bleeptrack/picoplanet/example/platformio/variants/bleeptrack_picoplanet/variant.h

/*
  Copyright (c) 2014-2015 Arduino LLC.  All right reserved.

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
  You should have received a copy of the GNU Lesser General Public
  License along with this library; if not, write to the Free Software
  Foundation, Inc., 51 Franklin St, Fifth Floor, Boston, MA  02110-1301  USA
*/

#ifndef _VARIANT_ARDUINO_ZERO_
#define _VARIANT_ARDUINO_ZERO_

// The definitions here needs a SAMD core >=1.6.6
#define ARDUINO_SAMD_VARIANT_COMPLIANCE 10606

/*----------------------------------------------------------------------------
 *        Definitions
 *----------------------------------------------------------------------------*/

/** Frequency of the board main oscillator */
#define VARIANT_MAINOSC		(32768ul)

/** Master clock frequency */
#define VARIANT_MCK	(F_CPU)

/*----------------------------------------------------------------------------
 *        Headers
 *----------------------------------------------------------------------------*/

#include "WVariant.h"

#ifdef __cplusplus
#include "SERCOM.h"
#include "Uart.h"
#endif // __cplusplus

#ifdef __cplusplus
extern "C"
{
#endif // __cplusplus

/*----------------------------------------------------------------------------
 *        Pins
 *----------------------------------------------------------------------------*/

// Number of pins defined in PinDescription array
#define PINS_COUNT           (22u)
#define NUM_DIGITAL_PINS     (22u)
#define NUM_ANALOG_INPUTS    (5u)
#define NUM_ANALOG_OUTPUTS   (1u)
#define analogInputToDigitalPin(p)  ((p < 5u) ? (p) + PIN_A0 : -1)

#define digitalPinToPort(P)        ( &(PORT->Group[g_APinDescription[P].ulPort]) )
#define digitalPinToBitMask(P)     ( 1 << g_APinDescription[P].ulPin )
//#define analogInPinToBit(P)        ( )
#define portOutputRegister(port)   ( &(port->OUT.reg) )
#define portInputRegister(port)    ( &(port->IN.reg) )
#define portModeRegister(port)     ( &(port->DIR.reg) )
#define digitalPinHasPWM(P)        ( g_APinDescription[P].ulPWMChannel != NOT_ON_PWM || g_APinDescription[P].ulTCChannel != NOT_ON_TIMER )

/*
 * digitalPinToTimer(..) is AVR-specific and is not defined for SAMD
 * architecture. If you need to check if a pin supports PWM you must
 * use digitalPinHasPWM(..).
 *
 * https://github.com/arduino/Arduino/issues/1833
 */
// #define digitalPinToTimer(P)

// PINs
#define PIN_D1                   (1u)
#define PIN_D2                   (2u)
#define PIN_D3                   (3u)
#define PIN_D4                   (4u)
#define PIN_D5                   (5u)
#define PIN_D6                   (6u)
#define PIN_D7                   (7u)
#define PIN_NC                   (0u)
#define PIN_SWCLK                (19u)
#define PIN_SWDIO                (20u)

static const uint8_t D1  = PIN_D1;
static const uint8_t D2  = PIN_D2;
static const uint8_t D3  = PIN_D3;
static const uint8_t D4  = PIN_D4;
static const uint8_t D5  = PIN_D5;
static const uint8_t D6  = PIN_D6;
static const uint8_t D7  = PIN_D7;
static const uint8_t SWCLK  = PIN_SWCLK;
static const uint8_t SWDIO  = PIN_SWDIO;

// LEDs
#define PIN_LED_G            PIN_D5
#define PIN_LED_R            PIN_D6
#define PIN_LED_B            PIN_D7
#define PIN_LED_13           PIN_LED_R
#define PIN_LED_RXL          PIN_NC // or LED_x if you want it to flash with Serial()
#define PIN_LED_TXL          PIN_NC // or LED_x if you want it to flash with Serial()
#define PIN_LED              PIN_LED_R
#define PIN_LED2             PIN_LED_G
#define PIN_LED3             PIN_LED_B
#define LED_BUILTIN          PIN_LED_R

static const uint8_t LED_R  = PIN_LED_R;
static const uint8_t LED_G  = PIN_LED_G;
static const uint8_t LED_B  = PIN_LED_B;


/*
 * Analog pins
 */
#define PIN_A0               (8ul)
#define PIN_A1               (PIN_A0 + 1)
#define PIN_A2               (PIN_A0 + 2)
#define PIN_A3               (PIN_A0 + 3)
#define PIN_A4               (PIN_A0 + 4)
#define PIN_DAC0             PIN_A0
#define TOUCH1               PIN_A0
#define TOUCH2               PIN_A1
#define TOUCH3               PIN_A2

static const uint8_t A0  = PIN_A0;
static const uint8_t A1  = PIN_A1;
static const uint8_t A2  = PIN_A2;
static const uint8_t A3  = PIN_A3;
static const uint8_t A4  = PIN_A4;
static const uint8_t DAC0 = PIN_DAC0;

#define ADC_RESOLUTION		12

/*
 * Serial interfaces
 */

// Serial1 (sercom 0)
#define PIN_SERIAL1_RX       (22u)
#define PAD_SERIAL1_RX       SERCOM_RX_PAD_1
#define PIN_SERIAL1_TX       (21u)
#define PAD_SERIAL1_TX       UART_TX_PAD_0

/*
 * SPI Interfaces
 */
#define SPI_INTERFACES_COUNT 1

#define PIN_SPI_MISO         (19u)
#define PIN_SPI_MOSI         (3u)
#define PIN_SPI_SCK          (4u)
#define PERIPH_SPI           sercom1
#define PAD_SPI_TX           SPI_PAD_0_SCK_1
#define PAD_SPI_RX           SERCOM_RX_PAD_2

static const uint8_t SS	  = PIN_NC ;
static const uint8_t MOSI = PIN_SPI_MOSI ;
static const uint8_t MISO = PIN_SPI_MISO ;
static const uint8_t SCK  = PIN_SPI_SCK ;

/*
 * Wire Interfaces
 */
#define WIRE_INTERFACES_COUNT 1

#define PIN_WIRE_SDA         (1u)
#define PIN_WIRE_SCL         (2u)
#define PERIPH_WIRE          sercom2
#define WIRE_IT_HANDLER      SERCOM2_Handler

static const uint8_t SDA = PIN_WIRE_SDA;
static const uint8_t SCL = PIN_WIRE_SCL;

/*
 * USB
 */
#define PIN_USB_HOST_ENABLE (16ul)
#define PIN_USB_DM          (17ul)
#define PIN_USB_DP          (18ul)

#ifdef __cplusplus
}
#endif

/*----------------------------------------------------------------------------
 *        Arduino objects - C++ only
 *----------------------------------------------------------------------------*/

#ifdef __cplusplus

/*	=========================
 *	===== SERCOM DEFINITION
 *	=========================
*/
extern SERCOM sercom0;
extern SERCOM sercom1;
extern SERCOM sercom2;
extern SERCOM sercom3;

extern Uart Serial1;

#endif

// These serial port names are intended to allow libraries and architecture-neutral
// sketches to automatically default to the correct port name for a particular type
// of use.  For example, a GPS module would normally connect to SERIAL_PORT_HARDWARE_OPEN,
// the first hardware serial port whose RX/TX pins are not dedicated to another use.
//
// SERIAL_PORT_MONITOR        Port which normally prints to the Arduino Serial Monitor
//
// SERIAL_PORT_USBVIRTUAL     Port which is USB virtual serial
//
// SERIAL_PORT_LINUXBRIDGE    Port which connects to a Linux system via Bridge library
//
// SERIAL_PORT_HARDWARE       Hardware serial port, physical RX & TX pins.
//
// SERIAL_PORT_HARDWARE_OPEN  Hardware serial ports which are open for use.  Their RX & TX
//                            pins are NOT connected to anything by default.
#define SERIAL_PORT_USBVIRTUAL      Serial
#define SERIAL_PORT_MONITOR         Serial
// Serial has no physical pins broken out, so it's not listed as HARDWARE port
#define SERIAL_PORT_HARDWARE        Serial1
#define SERIAL_PORT_HARDWARE_OPEN   Serial1

#endif /* _VARIANT_ARDUINO_ZERO_ */
