bleeptrack/picoplanet/example/platformio/variants/bleeptrack_picoplanet/variant.cpp

/*
  Copyright (c) 2014-2015 Arduino LLC.  All right reserved.

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
  You should have received a copy of the GNU Lesser General Public
  License along with this library; if not, write to the Free Software
  Foundation, Inc., 51 Franklin St, Fifth Floor, Boston, MA  02110-1301  USA
*/

#include "variant.h"

/*
 * Pins descriptions
 */
const PinDescription g_APinDescription[]=
{
  // Based on https://github.com/adafruit/ArduinoCore-samd/blob/master/variants/trinket_m0/variant.cpp
  // and Atmel SAM D21E / SAM D21G / SAM D21J [DATASHEET] Table 7-1. PORT Function Multiplexing (Page 31)
  // PicoPlanet Board Layout:
  // LABEL           PIN    SERCOM            SERCOM_ALT
  // D1,A3,SDA,TX    PA08   SERCOM0 PAD 0     SERCOM2 PAD 0
  // D2,A4,SCL,RX    PA09   SERCOM0 PAD 1     SERCOM2 PAD 1
  // D3,MOSI         PA16   SERCOM1 PAD 0     SERCOM3 PAD 0
  // D4,SCK          PA17   SERCOM1 PAD 1     SERCOM3 PAD 1
  // D5,LED_G        PA05
  // D6,LED_R        PA06
  // D7,LED_B        PA07
  // A0,TOUCH1       PA03
  // A1,TOUCH2       PA02
  // A2,TOUCH3       PA04
  // SWCLK,MISO      PA30                     SERCOM1 PAD 2
  // SWDIO           PA31                     SERCOM1 PAD 3

  // 0, NC
  { NOT_A_PORT, 99, PIO_NOT_A_PIN, (PIN_ATTR_NONE), No_ADC_Channel, NOT_ON_PWM, NOT_ON_TIMER, EXTERNAL_INT_NONE },
  // 1-7, D1-D7, I2C via SERCOM2, SPI via SERCOM1
  { PORTA,  8, PIO_SERCOM_ALT, (PIN_ATTR_DIGITAL|PIN_ATTR_ANALOG|PIN_ATTR_PWM|PIN_ATTR_TIMER), ADC_Channel16, PWM0_CH0, TCC0_CH0, EXTERNAL_INT_NMI },
  { PORTA,  9, PIO_SERCOM_ALT, (PIN_ATTR_DIGITAL|PIN_ATTR_ANALOG|PIN_ATTR_PWM|PIN_ATTR_TIMER), ADC_Channel17, PWM0_CH1, TCC0_CH1, EXTERNAL_INT_9 },
  { PORTA, 16, PIO_SERCOM, (PIN_ATTR_DIGITAL), No_ADC_Channel, NOT_ON_PWM, NOT_ON_TIMER, EXTERNAL_INT_NONE },
  { PORTA, 17, PIO_SERCOM, (PIN_ATTR_DIGITAL), No_ADC_Channel, NOT_ON_PWM, NOT_ON_TIMER, EXTERNAL_INT_NONE },
  { PORTA,  5, PIO_DIGITAL, (PIN_ATTR_DIGITAL|PIN_ATTR_ANALOG|PIN_ATTR_PWM|PIN_ATTR_TIMER), ADC_Channel5, PWM0_CH1, TCC0_CH1, EXTERNAL_INT_5 },
  { PORTA,  6, PIO_DIGITAL, (PIN_ATTR_DIGITAL|PIN_ATTR_ANALOG|PIN_ATTR_PWM|PIN_ATTR_TIMER), ADC_Channel6, PWM1_CH0, TCC1_CH0, EXTERNAL_INT_6 },
  { PORTA,  7, PIO_DIGITAL, (PIN_ATTR_DIGITAL|PIN_ATTR_ANALOG|PIN_ATTR_PWM|PIN_ATTR_TIMER), ADC_Channel7, PWM1_CH1, TCC1_CH1, EXTERNAL_INT_7 },
  // 8-12, A0-A4
  { PORTA,  3, PIO_ANALOG, (PIN_ATTR_ANALOG|PIN_ATTR_DIGITAL), ADC_Channel1, NOT_ON_PWM, NOT_ON_TIMER, EXTERNAL_INT_3 },
  { PORTA,  2, PIO_ANALOG, (PIN_ATTR_ANALOG|PIN_ATTR_DIGITAL), ADC_Channel0, NOT_ON_PWM, NOT_ON_TIMER, EXTERNAL_INT_2 },
  { PORTA,  4, PIO_ANALOG, (PIN_ATTR_ANALOG|PIN_ATTR_DIGITAL), ADC_Channel2, NOT_ON_PWM, NOT_ON_TIMER, EXTERNAL_INT_4 },
  { PORTA,  8, PIO_ANALOG, (PIN_ATTR_ANALOG|PIN_ATTR_DIGITAL|PIN_ATTR_PWM|PIN_ATTR_TIMER), ADC_Channel16, PWM0_CH0, TCC0_CH0, EXTERNAL_INT_NMI },
  { PORTA,  9, PIO_ANALOG, (PIN_ATTR_ANALOG|PIN_ATTR_DIGITAL|PIN_ATTR_PWM|PIN_ATTR_TIMER), ADC_Channel17, PWM0_CH1, TCC0_CH1, EXTERNAL_INT_9 },
  // 13, Typically an LED, so use PA07 (D7/LED_B) once again
  { PORTA,  7, PIO_DIGITAL, (PIN_ATTR_DIGITAL|PIN_ATTR_ANALOG|PIN_ATTR_PWM|PIN_ATTR_TIMER), ADC_Channel7, PWM1_CH1, TCC1_CH1, EXTERNAL_INT_7 },
  // 14-15
  { NOT_A_PORT, 99, PIO_NOT_A_PIN, (PIN_ATTR_NONE), No_ADC_Channel, NOT_ON_PWM, NOT_ON_TIMER, EXTERNAL_INT_NONE },
  { NOT_A_PORT, 99, PIO_NOT_A_PIN, (PIN_ATTR_NONE), No_ADC_Channel, NOT_ON_PWM, NOT_ON_TIMER, EXTERNAL_INT_NONE },
  // 16-18, USB
  { PORTA, 28, PIO_COM, PIN_ATTR_NONE, No_ADC_Channel, NOT_ON_PWM, NOT_ON_TIMER, EXTERNAL_INT_NONE }, // USB Host enable
  { PORTA, 24, PIO_COM, PIN_ATTR_NONE, No_ADC_Channel, NOT_ON_PWM, NOT_ON_TIMER, EXTERNAL_INT_NONE }, // USB/DM
  { PORTA, 25, PIO_COM, PIN_ATTR_NONE, No_ADC_Channel, NOT_ON_PWM, NOT_ON_TIMER, EXTERNAL_INT_NONE }, // USB/DP
  // 19-20, SWCLK & SWDIO, SPI via SERCOM1
  { PORTA, 30, PIO_SERCOM_ALT, PIN_ATTR_NONE, No_ADC_Channel, NOT_ON_PWM, NOT_ON_TIMER, EXTERNAL_INT_NONE },
  { PORTA, 31, PIO_SERCOM_ALT, PIN_ATTR_NONE, No_ADC_Channel, NOT_ON_PWM, NOT_ON_TIMER, EXTERNAL_INT_NONE },
  // 21-22, UART via SERCOM0 on D1,D2
  { PORTA,  8, PIO_SERCOM, (PIN_ATTR_DIGITAL|PIN_ATTR_PWM|PIN_ATTR_TIMER), ADC_Channel16, PWM0_CH0, TCC0_CH0, EXTERNAL_INT_NMI },
  { PORTA,  9, PIO_SERCOM, (PIN_ATTR_DIGITAL|PIN_ATTR_PWM|PIN_ATTR_TIMER), ADC_Channel17, PWM0_CH1, TCC0_CH1, EXTERNAL_INT_9 },
} ;

const void* g_apTCInstances[TCC_INST_NUM+TC_INST_NUM]={ TCC0, TCC1, TCC2, TC3, TC4, TC5 } ;

// Multi-serial objects instantiation
SERCOM sercom0( SERCOM0 ) ;
SERCOM sercom1( SERCOM1 ) ;
SERCOM sercom2( SERCOM2 ) ;
SERCOM sercom3( SERCOM3 ) ;

Uart Serial1( &sercom0, PIN_SERIAL1_RX, PIN_SERIAL1_TX, PAD_SERIAL1_RX, PAD_SERIAL1_TX ) ;

void SERCOM0_Handler()
{
  Serial1.IrqHandler();
}
